kholia/Si5351-Module-Clone-TCXO/Adafruit-Si5351A-v6/Screenshot 2025-03-18 at 10.27.32 PM.png

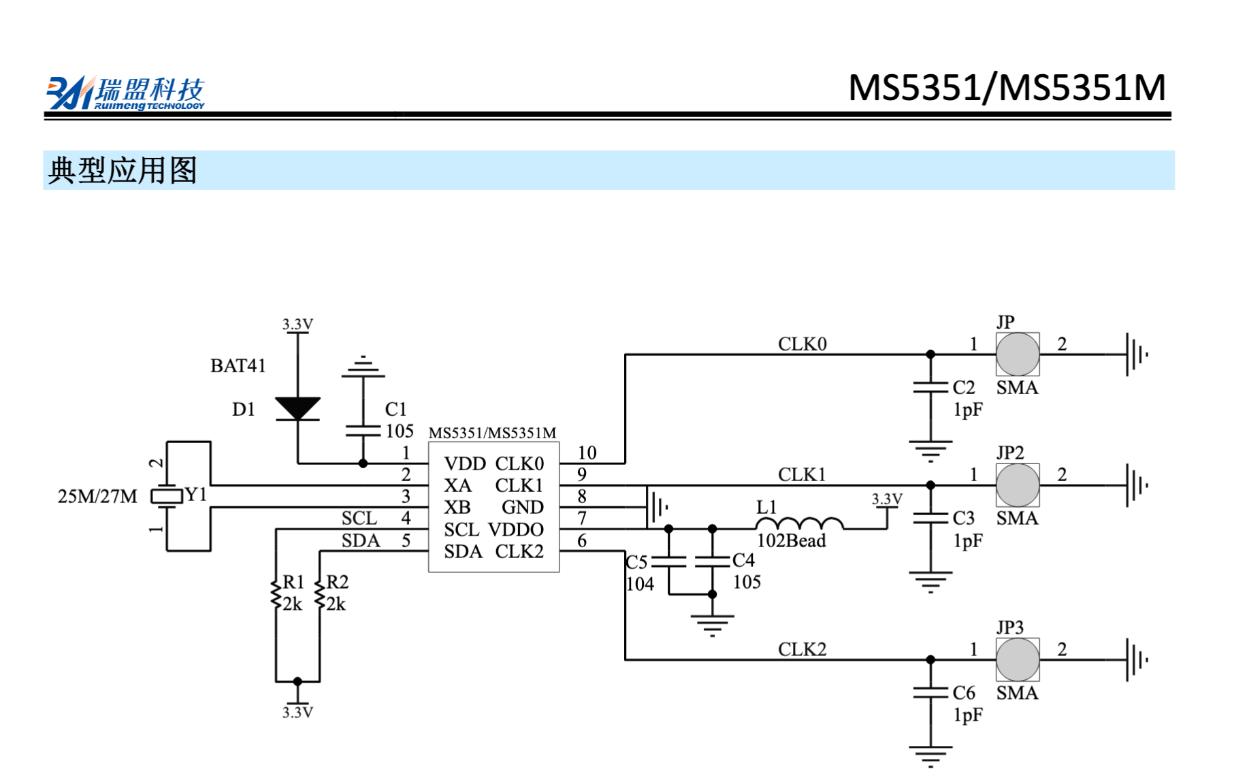
Adafruit-Si5351A-v6/Screenshot 2025-03-18 at 10.27.32 PM.png
