kholia/Si5351-Module-Clone-TCXO/datasheets/859ef0_23deba5b7bef447283ad6f0be6cf43f8~mv2.png

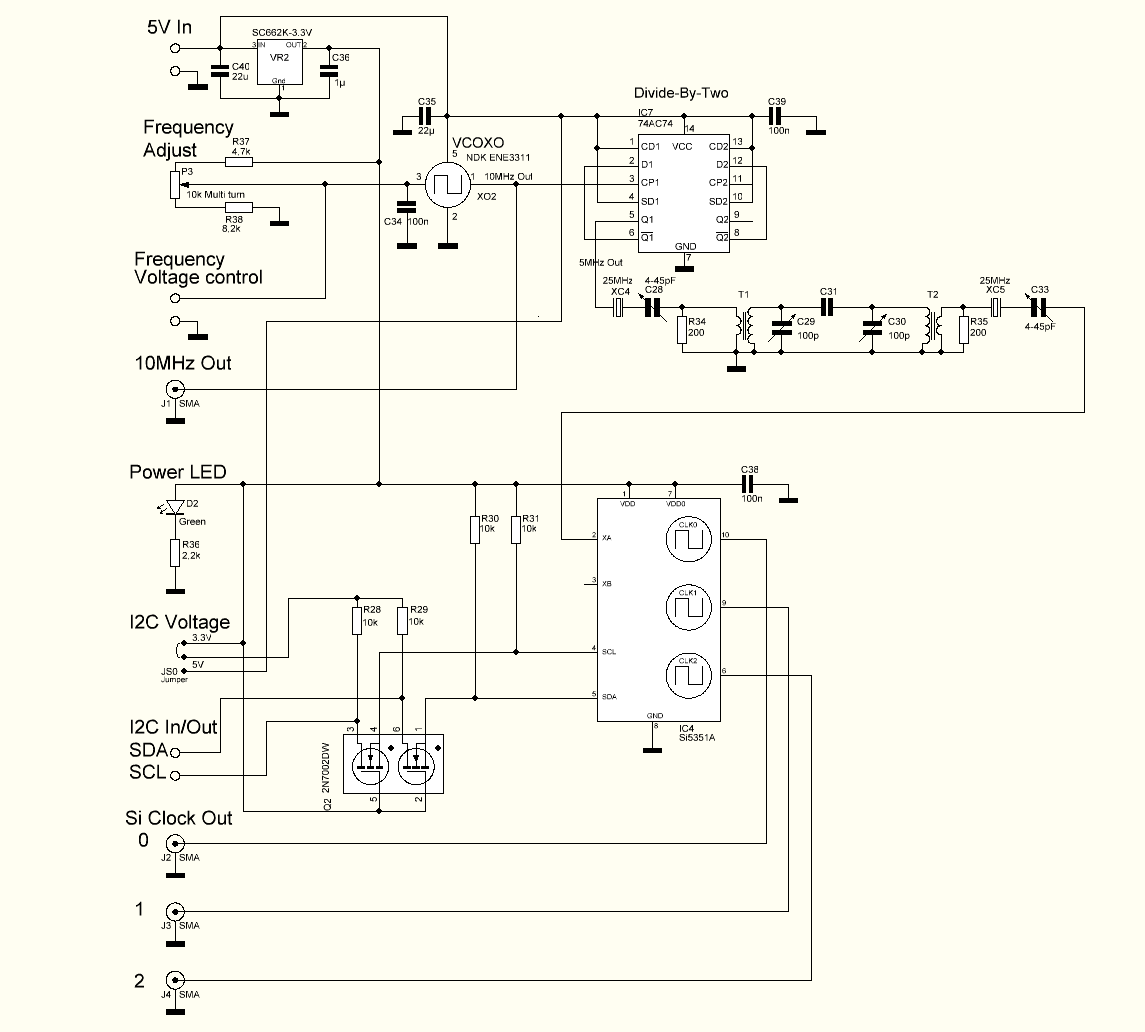
datasheets/859ef0_23deba5b7bef447283ad6f0be6cf43f8~mv2.png
