kholia/Si5351-Module-Clone-TCXO/datasheets/etc/Abracon_LLC_ATX-11-F-27.000MHZ-F05-T_12568.jpg

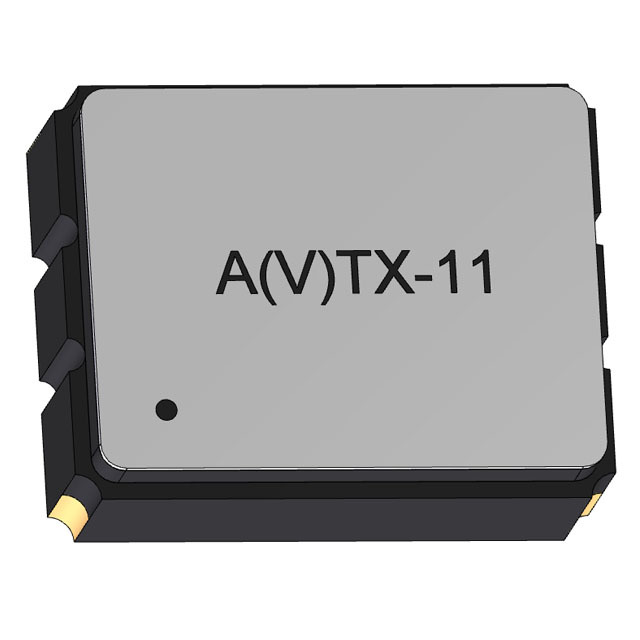
datasheets/etc/Abracon_LLC_ATX-11-F-27.000MHZ-F05-T_12568.jpg
