kholia/Si5351-Module-Clone-TCXO/datasheets/Screenshot_2022-11-21_21-57-31.png

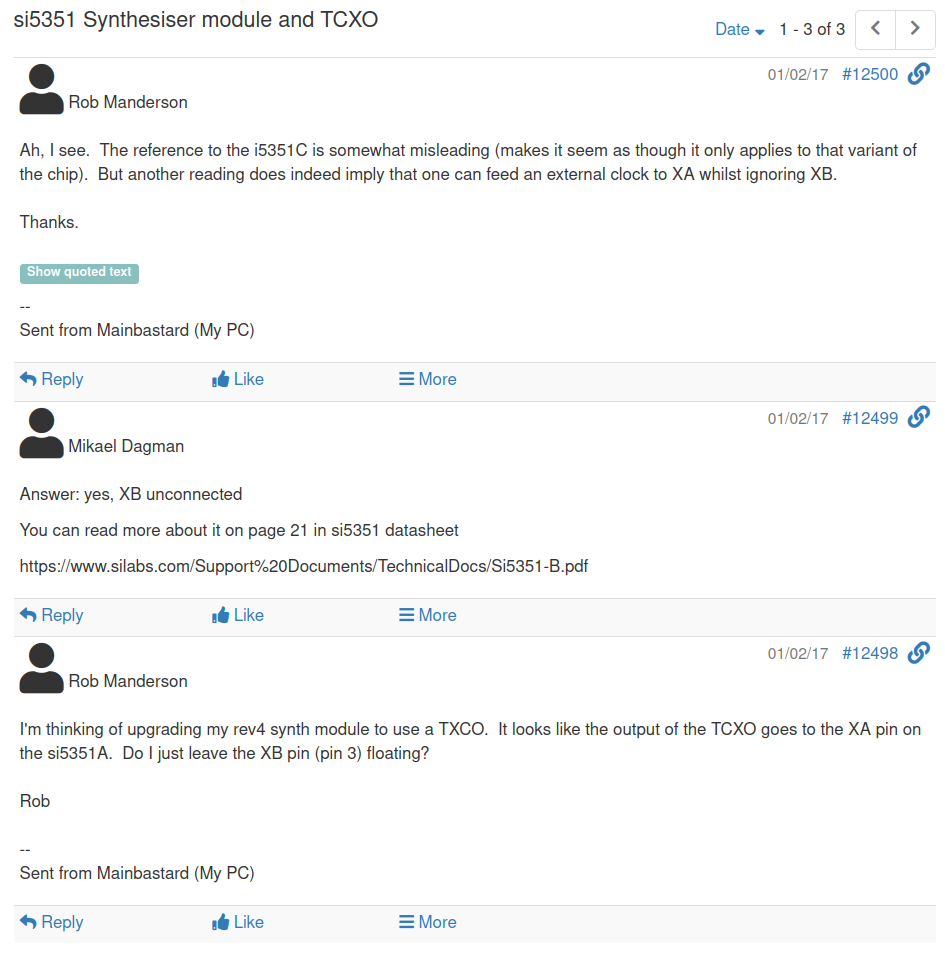
datasheets/Screenshot_2022-11-21_21-57-31.png
