kholia/Si5351-Module-Clone-TCXO/datasheets/Screenshot_2022-11-22_22-34-12.png

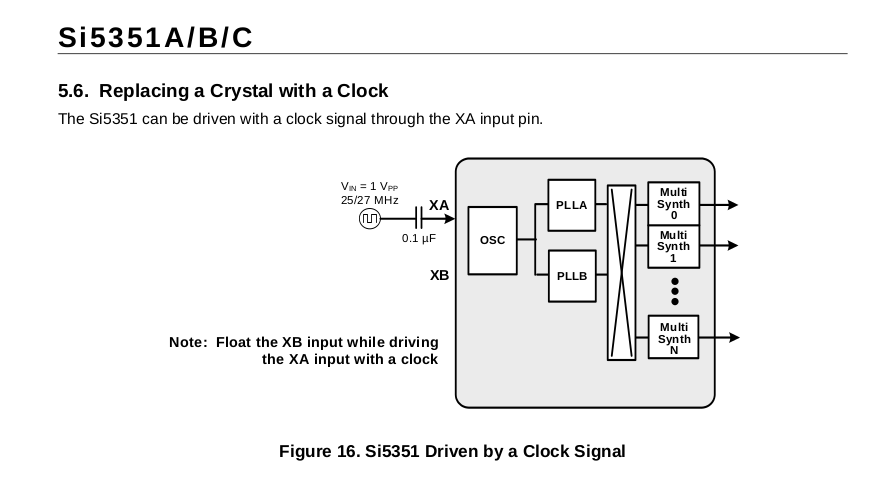
datasheets/Screenshot_2022-11-22_22-34-12.png
