kholia/Si5351-Module-Clone-TCXO/datasheets/Screenshot_2022-11-22_22-35-54.png

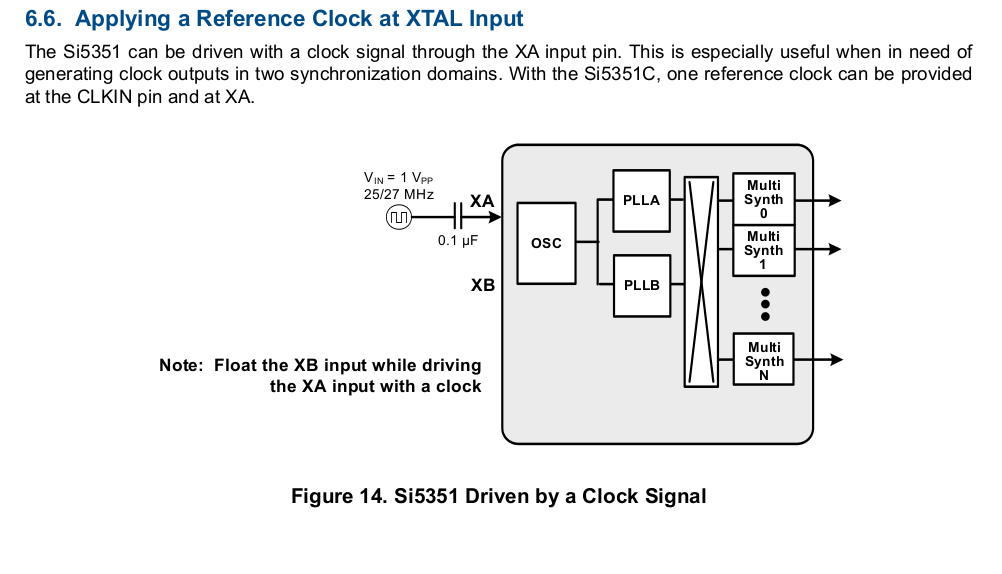
datasheets/Screenshot_2022-11-22_22-35-54.png
