kholia/Si5351-Module-Clone-TCXO/datasheets/Screenshot_2022-11-23_09-30-16.png

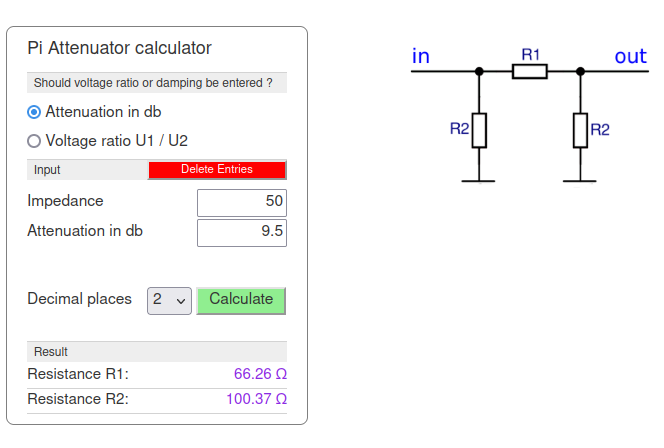
datasheets/Screenshot_2022-11-23_09-30-16.png
