kholia/Si5351-Module-Clone-TCXO/datasheets/Screenshot_2023-01-04_11-52-28.png

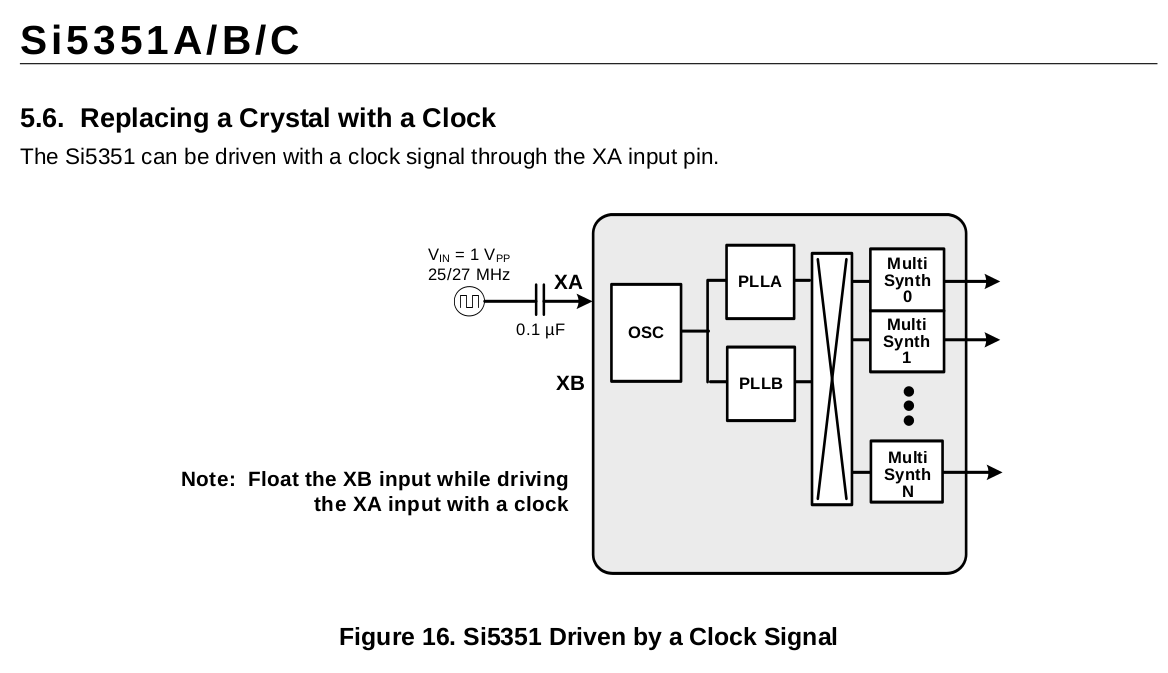
datasheets/Screenshot_2023-01-04_11-52-28.png
