kholia/Si5351-Module-Clone-TCXO/datasheets/Screenshot_2023-01-04_12-11-43.png

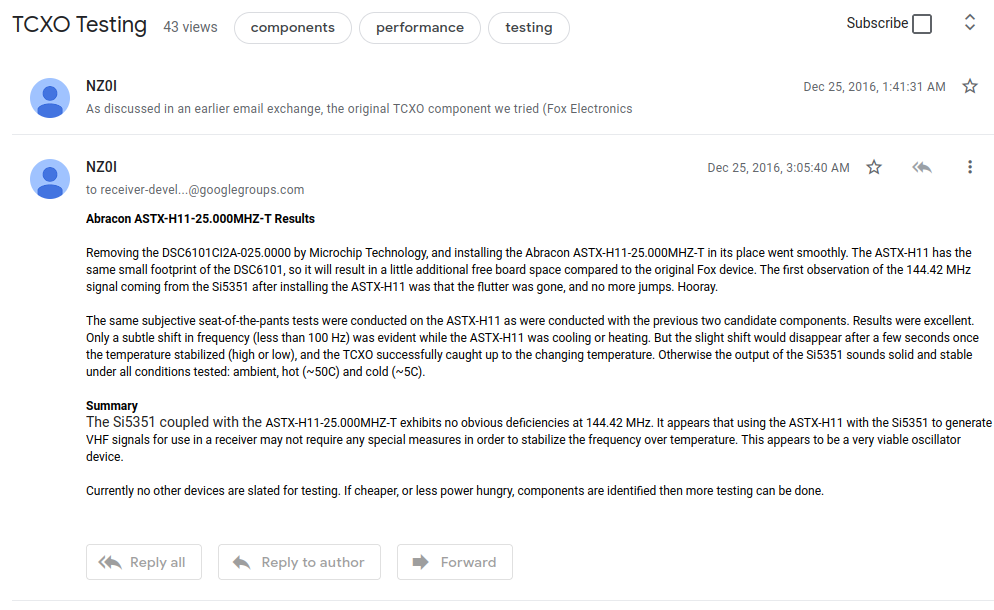
datasheets/Screenshot_2023-01-04_12-11-43.png
