kholia/Si5351-Module-Clone-TCXO/datasheets/Screenshot_2023-01-04_15-59-57.png

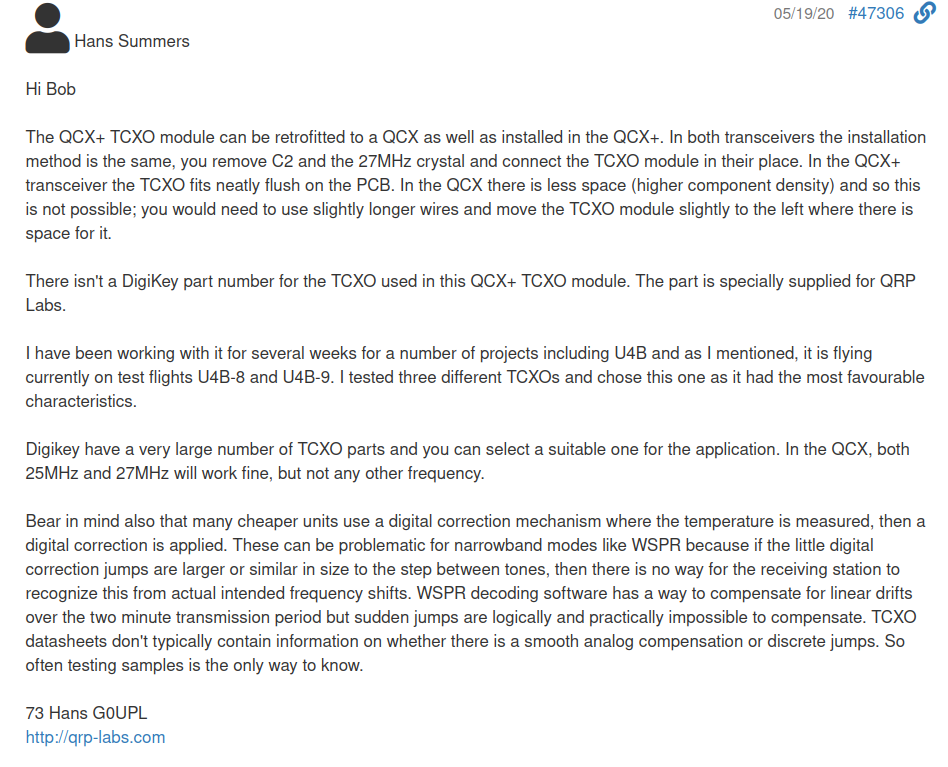
datasheets/Screenshot_2023-01-04_15-59-57.png
