kholia/Si5351-Module-Clone-TCXO/datasheets/Screenshot_2023-01-13_10-31-32.png

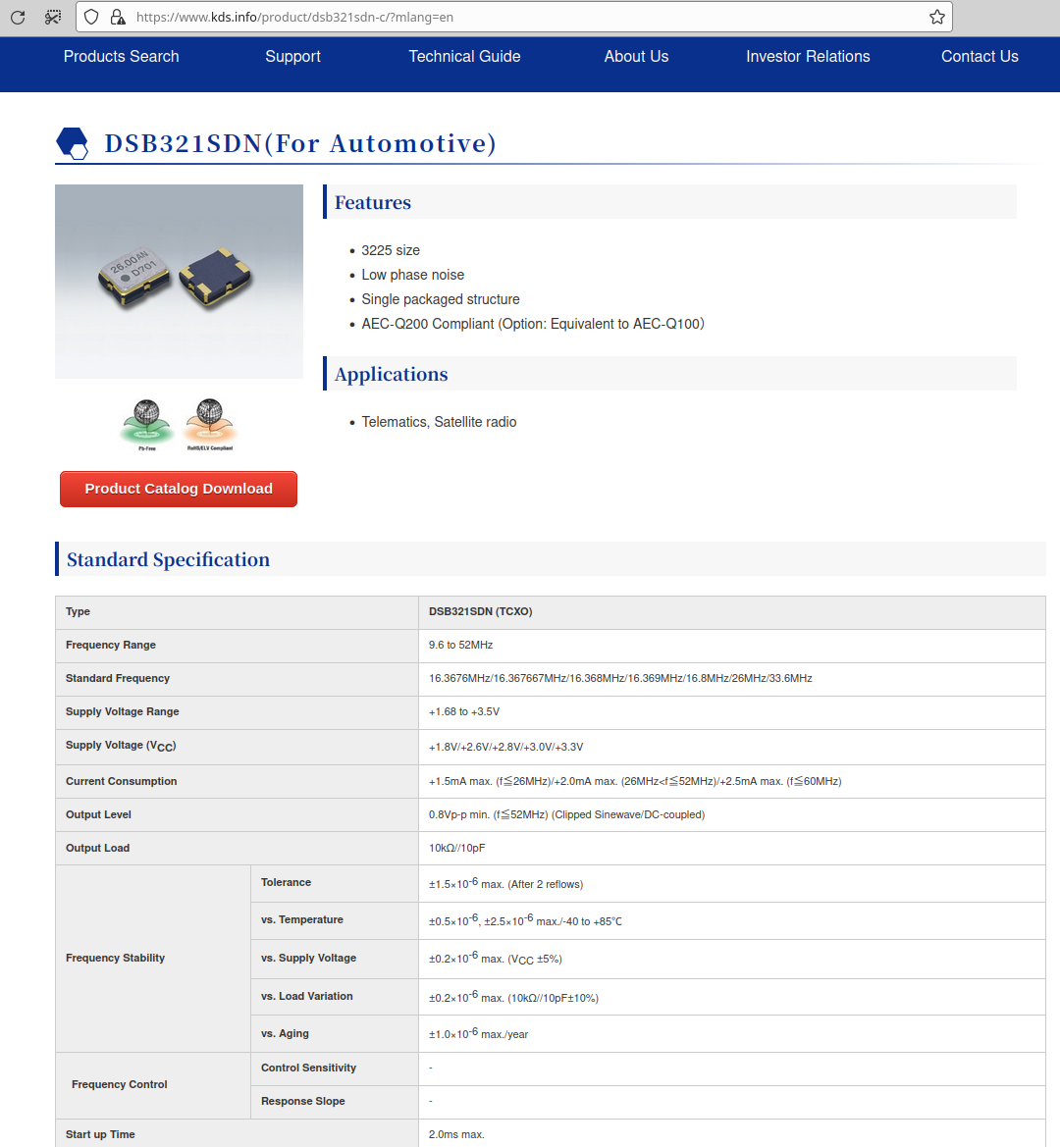
datasheets/Screenshot_2023-01-13_10-31-32.png
